quietprotocol/enclosures/GIZOisNT_Antenna/img/parts/adapter_sma_04.jpg

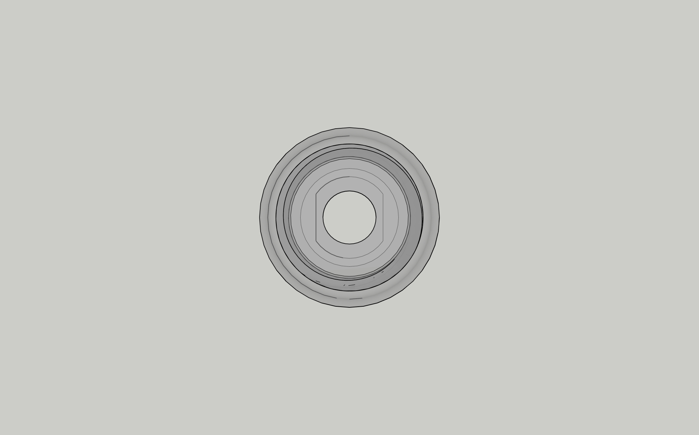
GIZOisNT_Antenna/img/parts/adapter_sma_04.jpg
