quietprotocol/enclosures/GIZOisNT_Antenna/model files/tube_200mm.stl

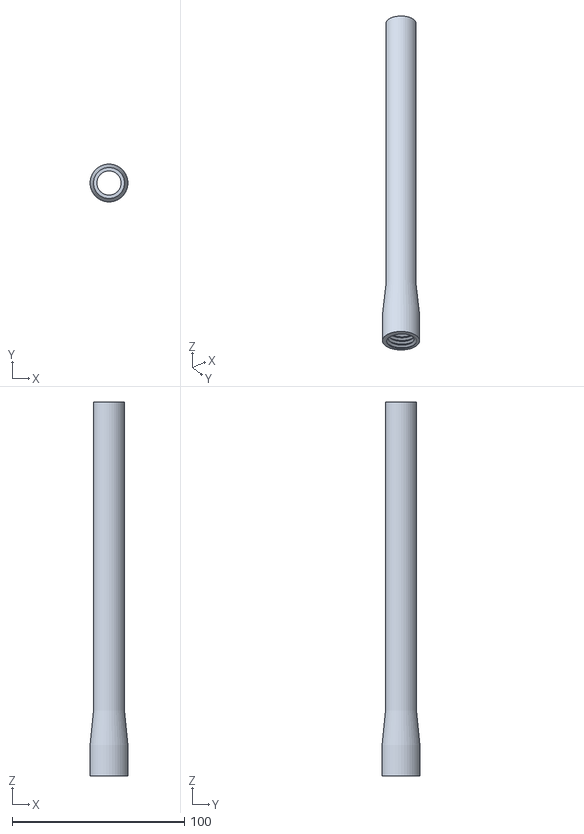
[picture p36: CAD file, 2026-02-08]
GIZOisNT_Antenna/model files/tube_200mm.stl
22.0 x 22.0 x 217.0
