quietprotocol/enclosures/OpenChubNET/stl/openMANET_enclosure_rpi4_ups_battery_rj45.stl

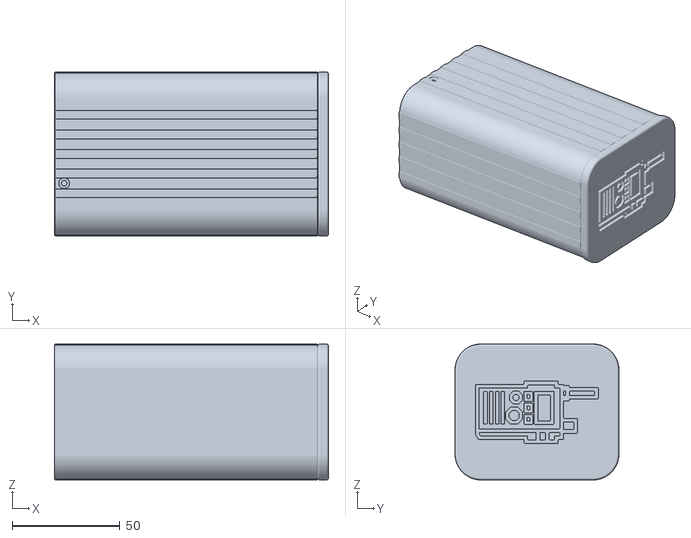
[picture p37: CAD file, 2025-12-15]
OpenChubNET/stl/openMANET_enclosure_rpi4_ups_battery_rj45.stl
127.0 x 76.0 x 63.0
