quietprotocol/enclosures/GIZOisNT_Antenna/model files/adapter_sma.stl

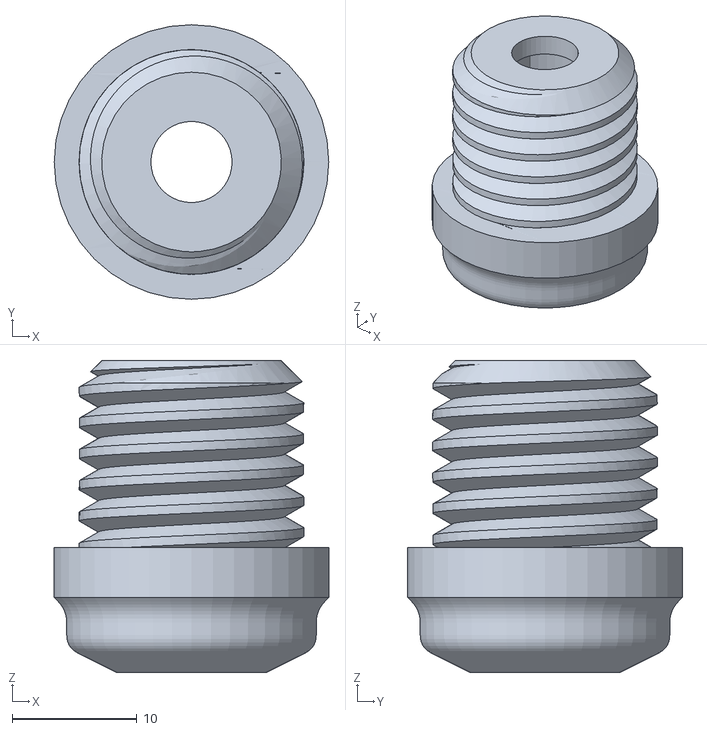
[picture p38: CAD file, 2026-02-08]
GIZOisNT_Antenna/model files/adapter_sma.stl
22.0 x 22.0 x 25.0
