quietprotocol/enclosures/OpenChubNET/stl/openMANET_stencil_top_base.stl

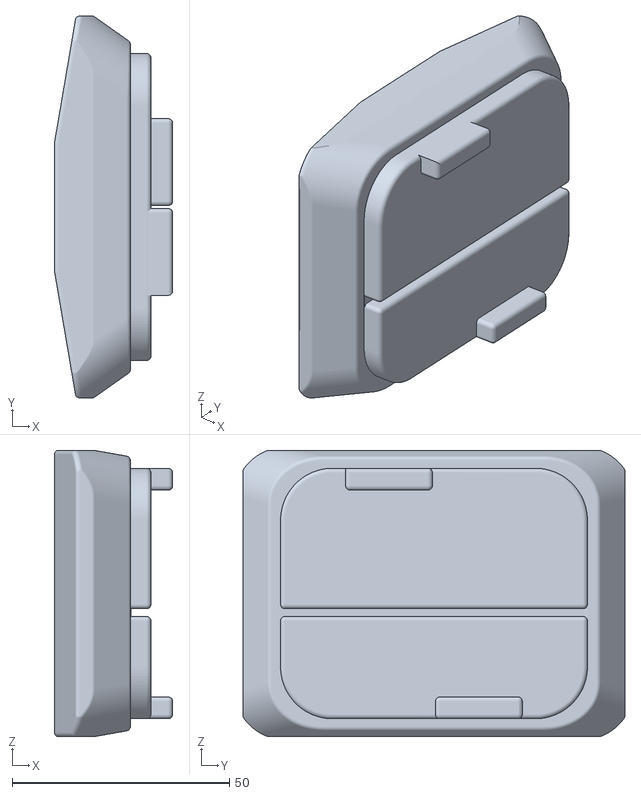
[picture p39: CAD file, 2025-12-15]
OpenChubNET/stl/openMANET_stencil_top_base.stl
27.2 x 88.0 x 66.0
