quietprotocol/enclosures/GetStarted/stl/open manet enclosure no ups hatch.stl

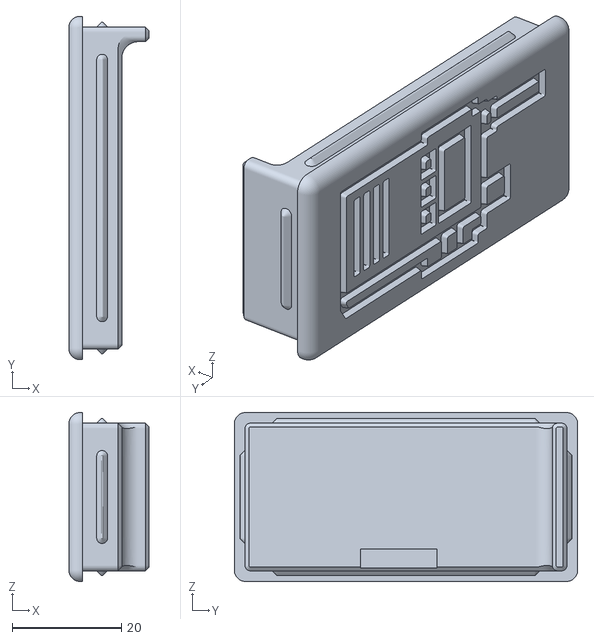
[picture p40: CAD file, 2025-11-13]
GetStarted/stl/open manet enclosure no ups hatch.stl
14.7 x 62.8 x 30.9
