quietprotocol/enclosures/GIZOisNT_Antenna/model files/tube_100mm.stl

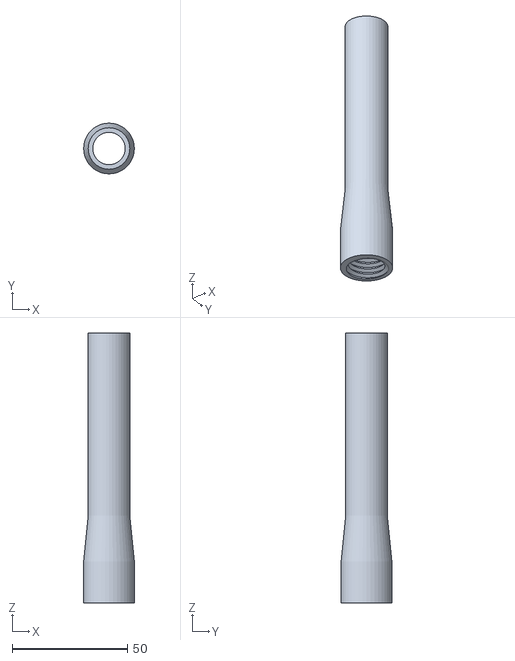
[picture p41: CAD file, 2026-02-08]
GIZOisNT_Antenna/model files/tube_100mm.stl
22.0 x 22.0 x 117.0
