quietprotocol/enclosures/OpenChubNET/stl/openMANET_stencil_sma_small.stl

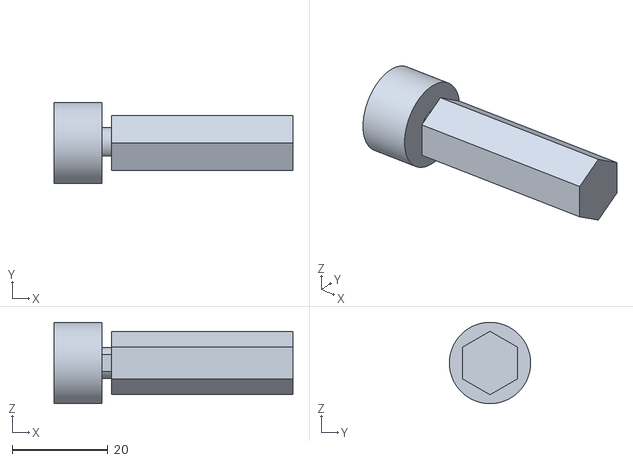
[picture p42: CAD file, 2025-12-15]
OpenChubNET/stl/openMANET_stencil_sma_small.stl
50.0 x 17.0 x 17.0
