quietprotocol/enclosures/OpenChubNET/stl/openMANET_mounting_plate.stl

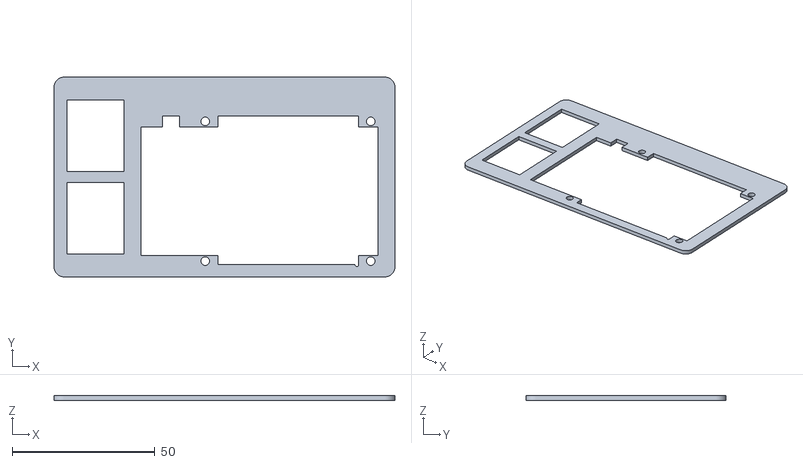
[picture p43: CAD file, 2025-11-21]
OpenChubNET/stl/openMANET_mounting_plate.stl
119.5 x 70.0 x 1.60
