quietprotocol/enclosures/OpenChubNET/stl/openMANET_stencil_top.stl

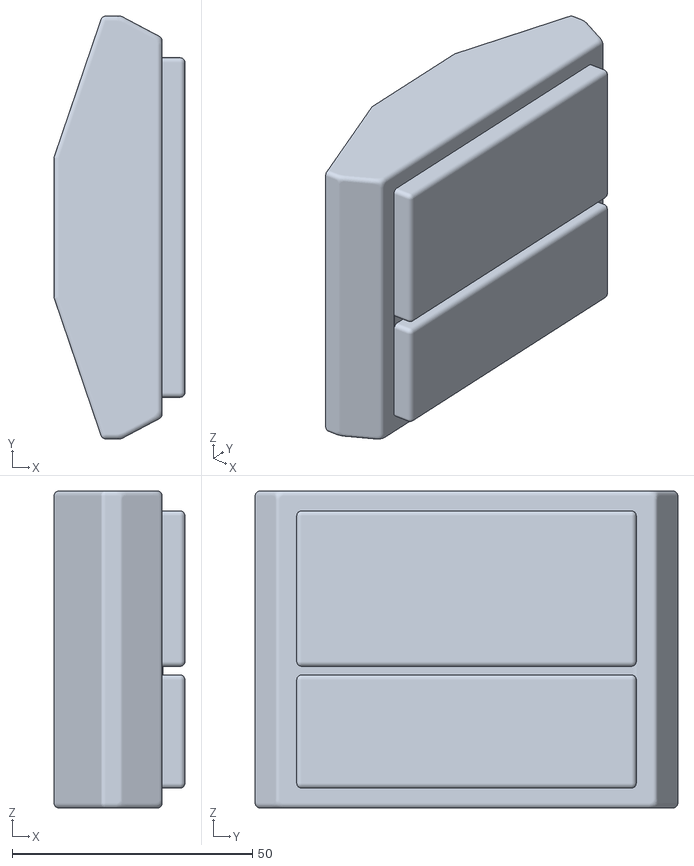
[picture p44: CAD file, 2025-11-21]
OpenChubNET/stl/openMANET_stencil_top.stl
27.2 x 88.0 x 66.0
