quietprotocol/enclosures/OpenChubNET/stl/openMANET_stencil_ntype.stl

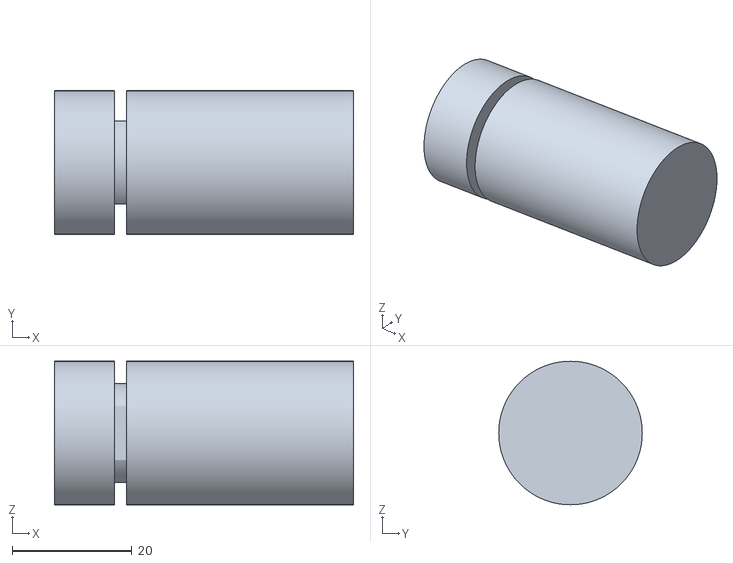
[picture p45: CAD file, 2025-11-21]
OpenChubNET/stl/openMANET_stencil_ntype.stl
50.0 x 24.0 x 24.0
