quietprotocol/enclosures/OpenChubNET/stl/openMANET_stencil_cazn_usb.stl

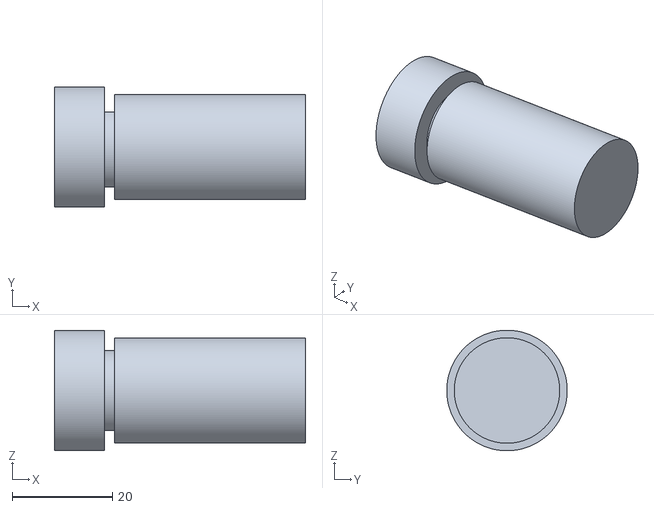
[picture p46: CAD file, 2025-11-21]
OpenChubNET/stl/openMANET_stencil_cazn_usb.stl
50.0 x 24.0 x 24.0
