quietprotocol/enclosures/OpenChubNET/stl/openMANET_stencil_cazn_rj45.stl

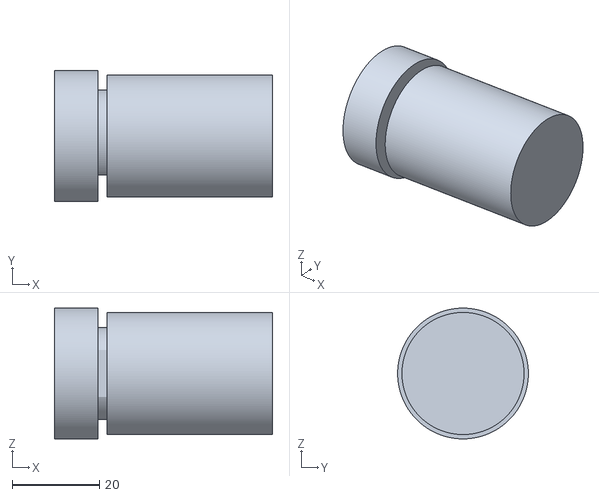
[picture p47: CAD file, 2025-11-21]
OpenChubNET/stl/openMANET_stencil_cazn_rj45.stl
50.0 x 30.0 x 30.0
