quietprotocol/enclosures/OpenChubNET/stl/openMANET_stencil_sma_large.stl

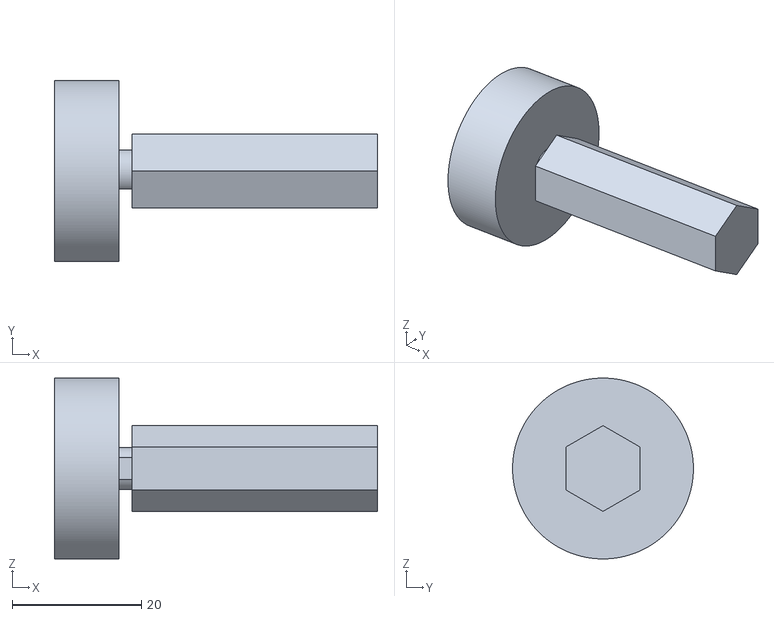
[picture p48: CAD file, 2025-11-21]
OpenChubNET/stl/openMANET_stencil_sma_large.stl
50.0 x 28.0 x 28.0
