quietprotocol/enclosures/GIZOisNT_Antenna/img/assembly/19.jpg

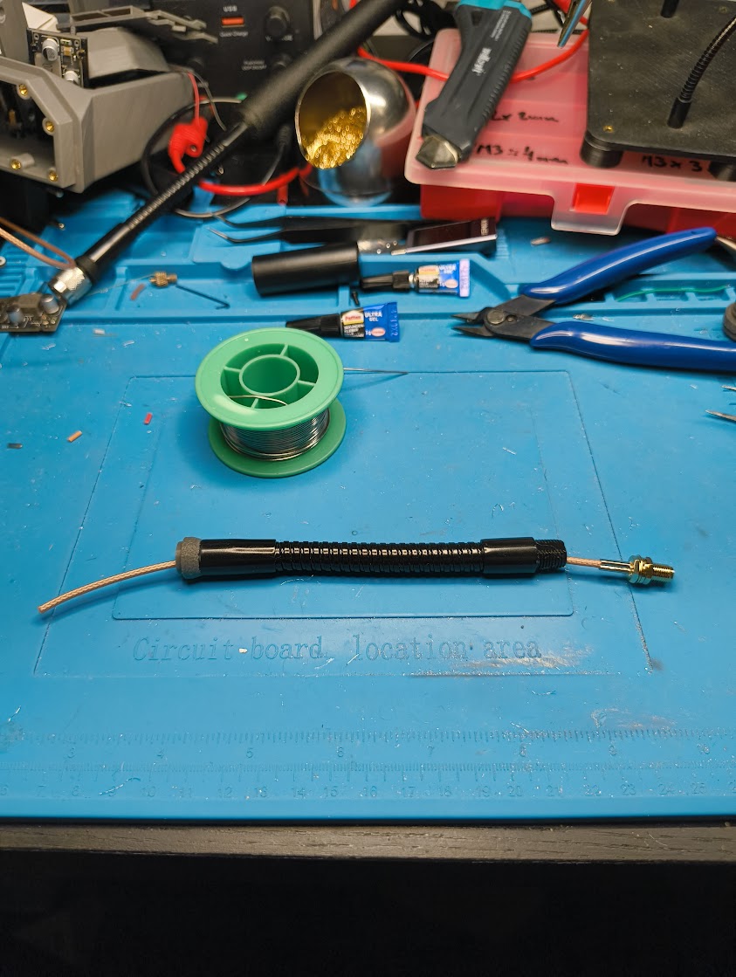
GIZOisNT_Antenna/img/assembly/19.jpg
